hhhlau/sd-5529-embedded-interaction/Assets and resources/Image.jpeg

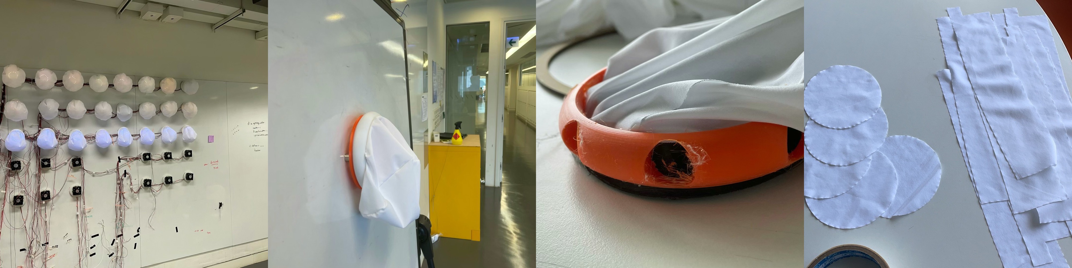
Assets and resources/Image.jpeg
