hhhlau/sd-5529-embedded-interaction/Assets and resources/IMG_0008.png

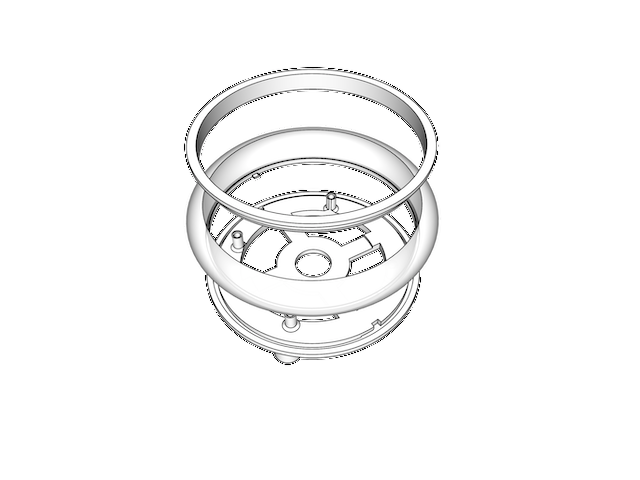
Assets and resources/IMG_0008.png
