hhhlau/sd-5529-embedded-interaction/Assets and resources/IMG_0011.png

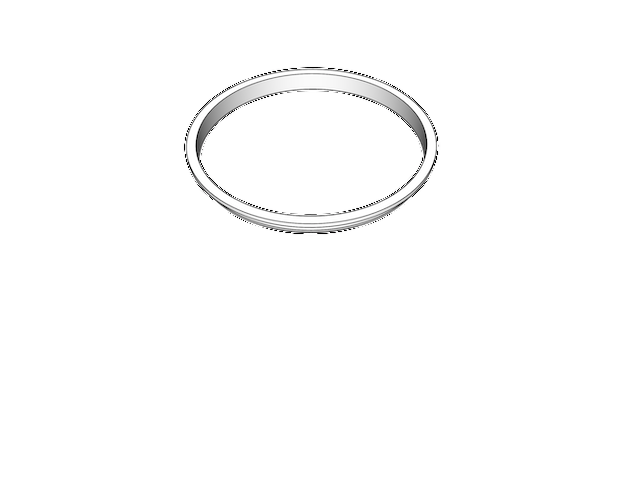
Assets and resources/IMG_0011.png
