hhhlau/sd-5529-embedded-interaction/Assets and resources/IMG_1431.JPG

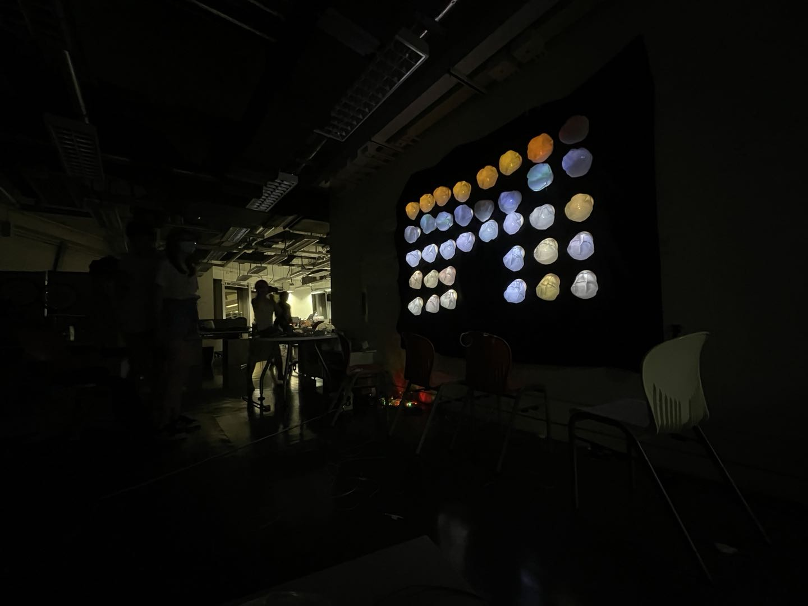
Assets and resources/IMG_1431.JPG
