hhhlau/sd-5529-embedded-interaction/Assets and resources/IMG_3083.png

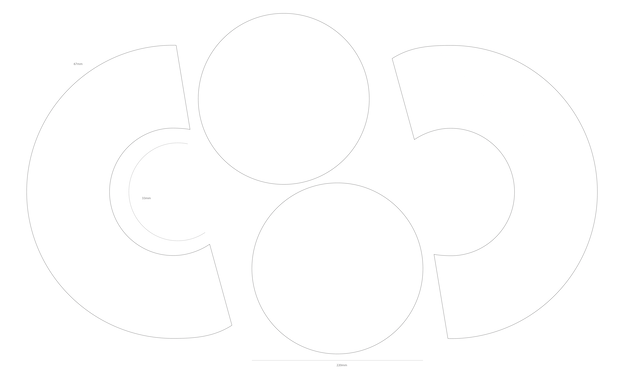
Assets and resources/IMG_3083.png
